uoaerg/dmx-arduino/dmxcontroller/dmxboard.h

/* DMXBoard */
#ifndef DMXBOARD_H
  #define DMXBOARD_H

  #define REV_II 2
  #define REV_IIIA 3

  // #define REV	REV_II 
  #define REV REV_IIIA

  // #pragma message "Board and software revision defined in dmxboard.h."
  #ifndef REV
    // #pragma message "Please set a board revision in dmxboard.h"
  #endif

  #define GIT "Release 1.0 (08-23 GF)"	/* please set manually before flashing */

  #if REV == REV_II
    #define DMXBOARDREV "dmxboard rev II"
  #endif

  #if REV == REV_IIIA
    #define DMXBOARDREV "dmxboard rev IIIA"
  #endif

#endif //  DMXBOARD_H
